Web3-Pi/Web3-Pi-UPS/docs/images/renders/front_3.png

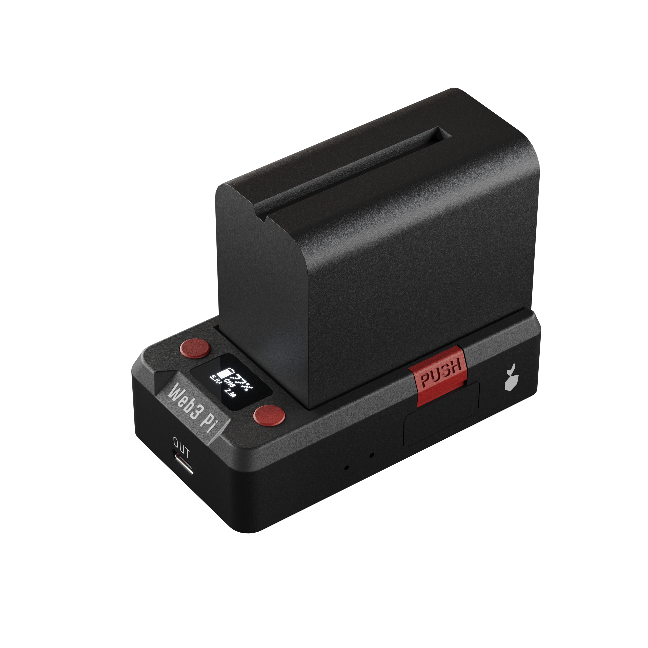
docs/images/renders/front_3.png
