Web3-Pi/Web3-Pi-UPS/firmware-ESP32-LTE-M/docs/SIM7080_1.jpg.webp

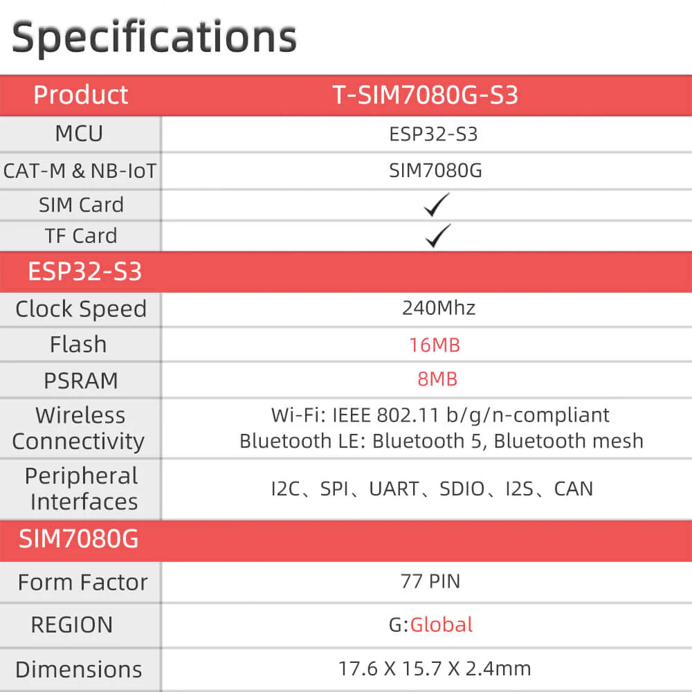
firmware-ESP32-LTE-M/docs/SIM7080_1.jpg.webp
