Web3-Pi/Web3-Pi-UPS/firmware-ESP32-LTE-M/docs/SIM7080_2_1.jpg.webp

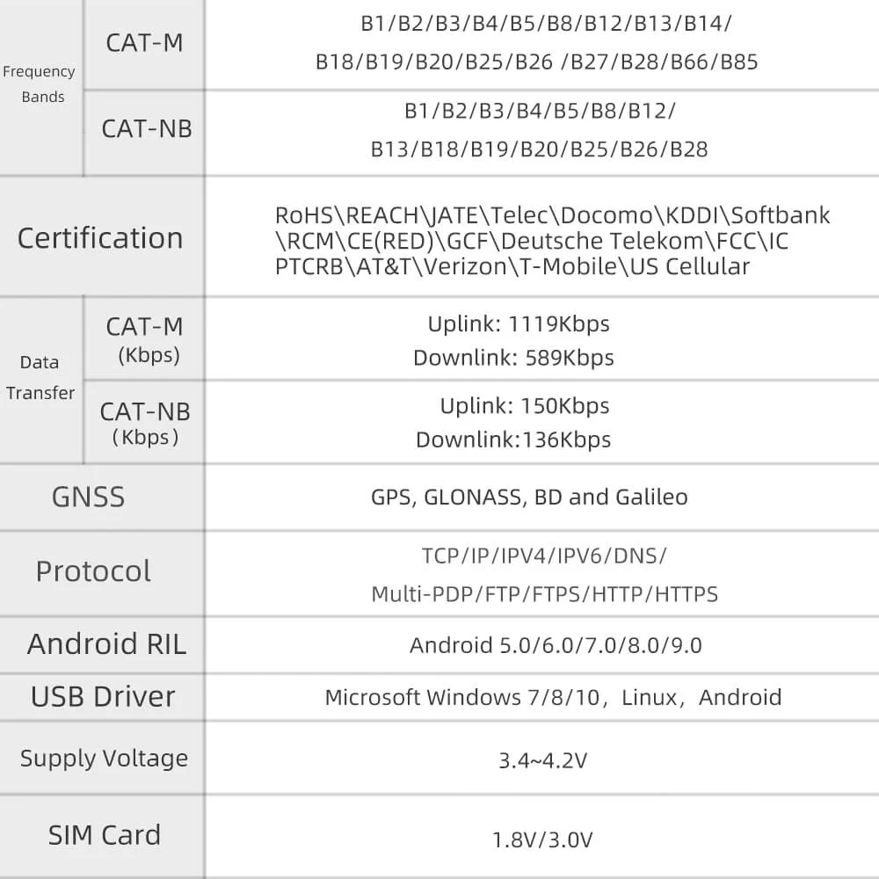
firmware-ESP32-LTE-M/docs/SIM7080_2_1.jpg.webp
