Web3-Pi/Web3-Pi-UPS/firmware-ESP32-LTE-M/docs/T-SIM7080G-S3-H606_8.jpg

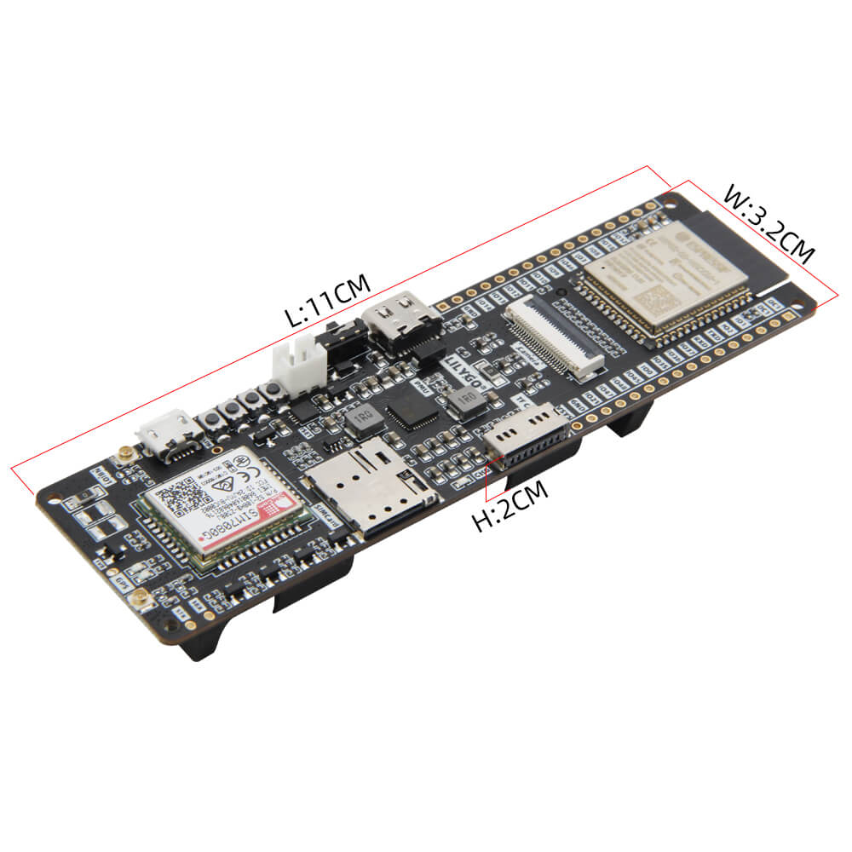
firmware-ESP32-LTE-M/docs/T-SIM7080G-S3-H606_8.jpg
