Web3-Pi/Web3-Pi-UPS/firmware-ESP32-LTE-M/docs/T-SIM7080G_Schematic.pdf

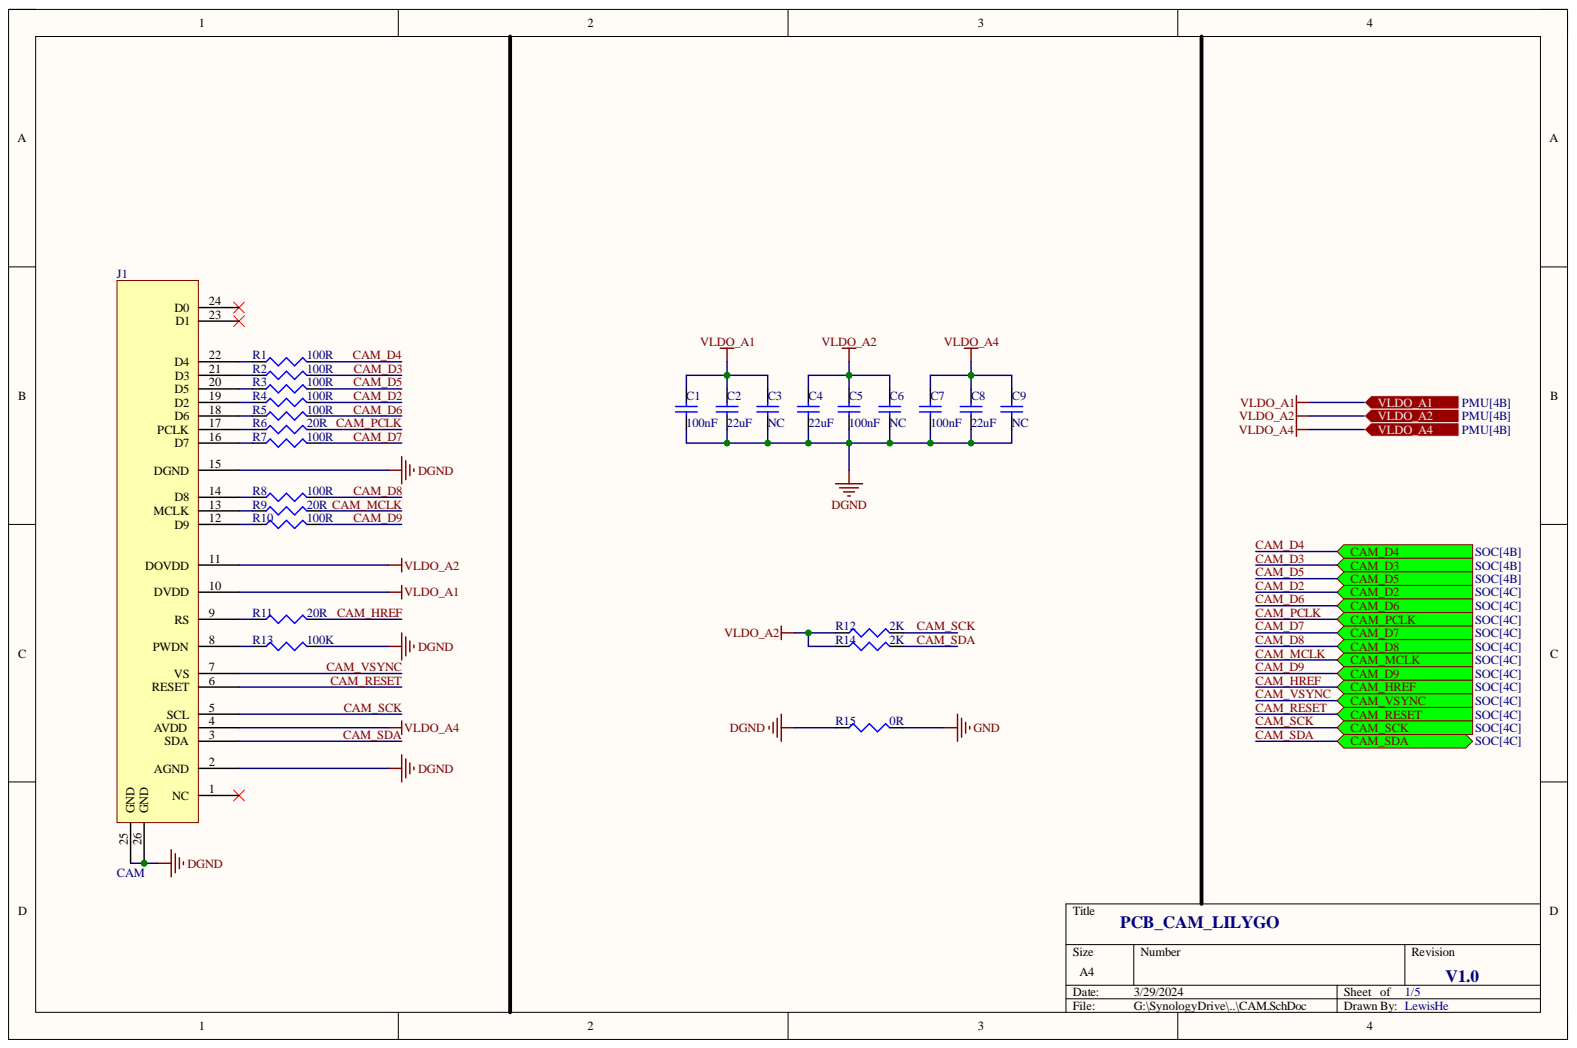
[picture p45: page 1]

Siz e A4 | Numb e r | R evisio n V1.

Da te : 3/29/202 4 | She et of
File : G:\SynologyDrive\. .\C AM . S c hD o c | Dr awn B y : Lewi s H e

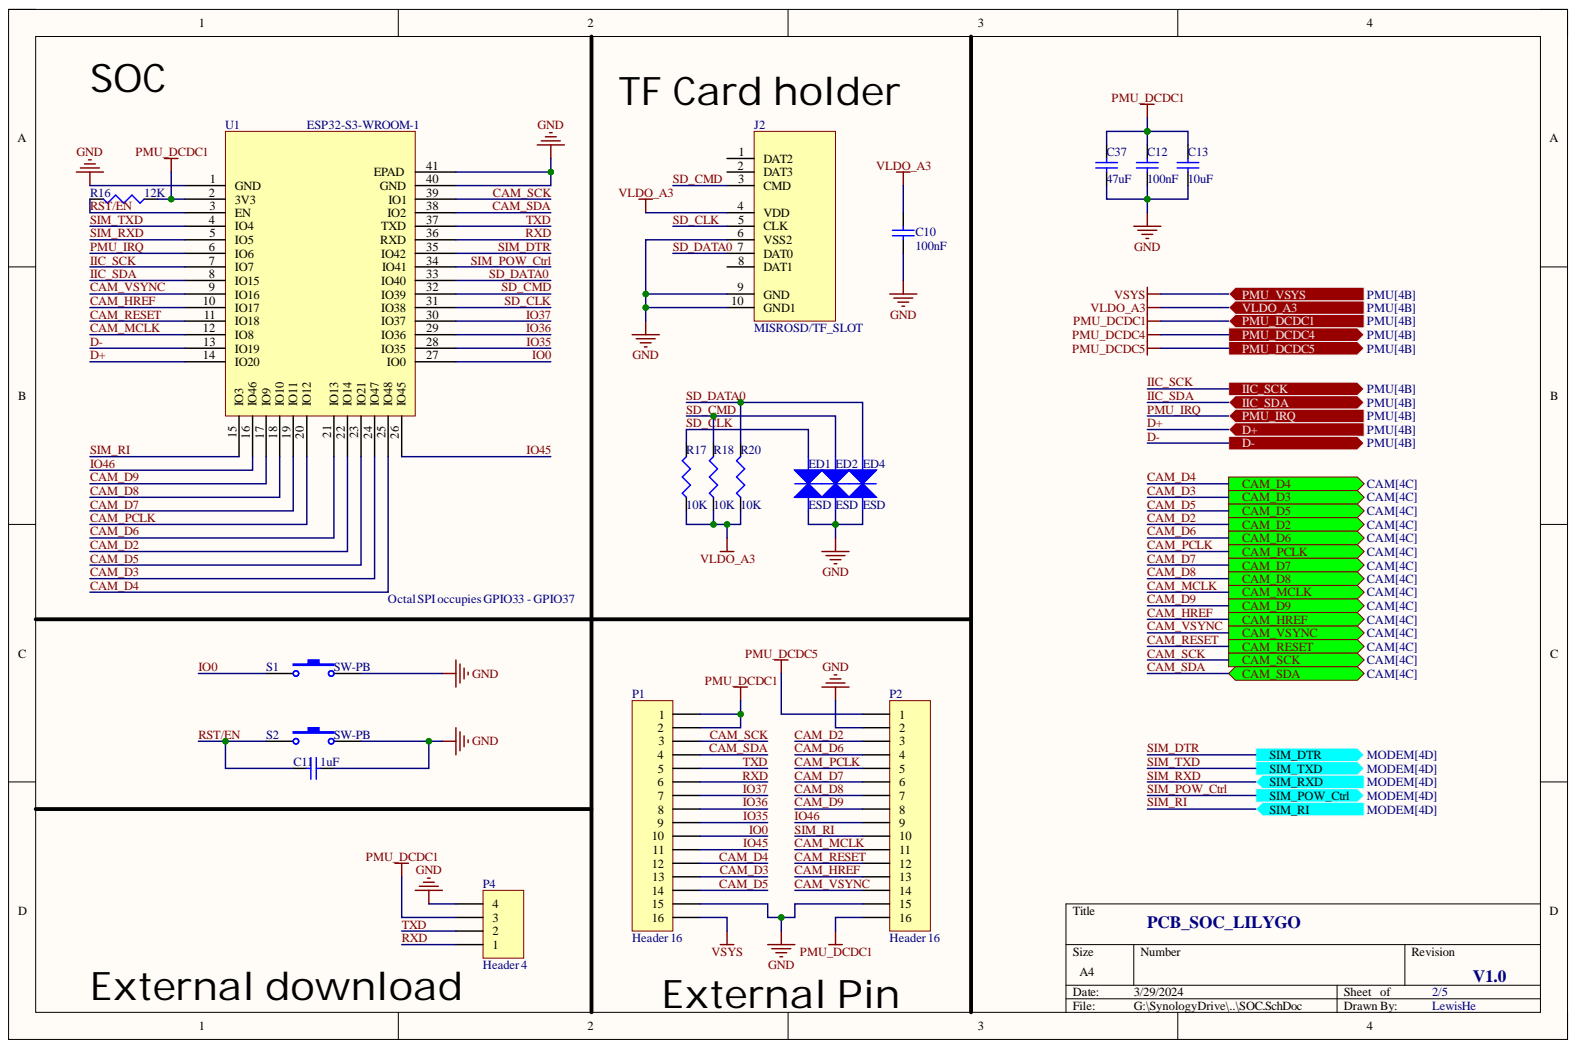
[picture p46: page 2]

2 | | CAM_S C K
3 | | CAM_S D A

Da te : 3/29/202 4 | She et of
File : G:\SynologyDrive\. .\S O C . S c hD o c | Dr awn B y : Lewi s H e

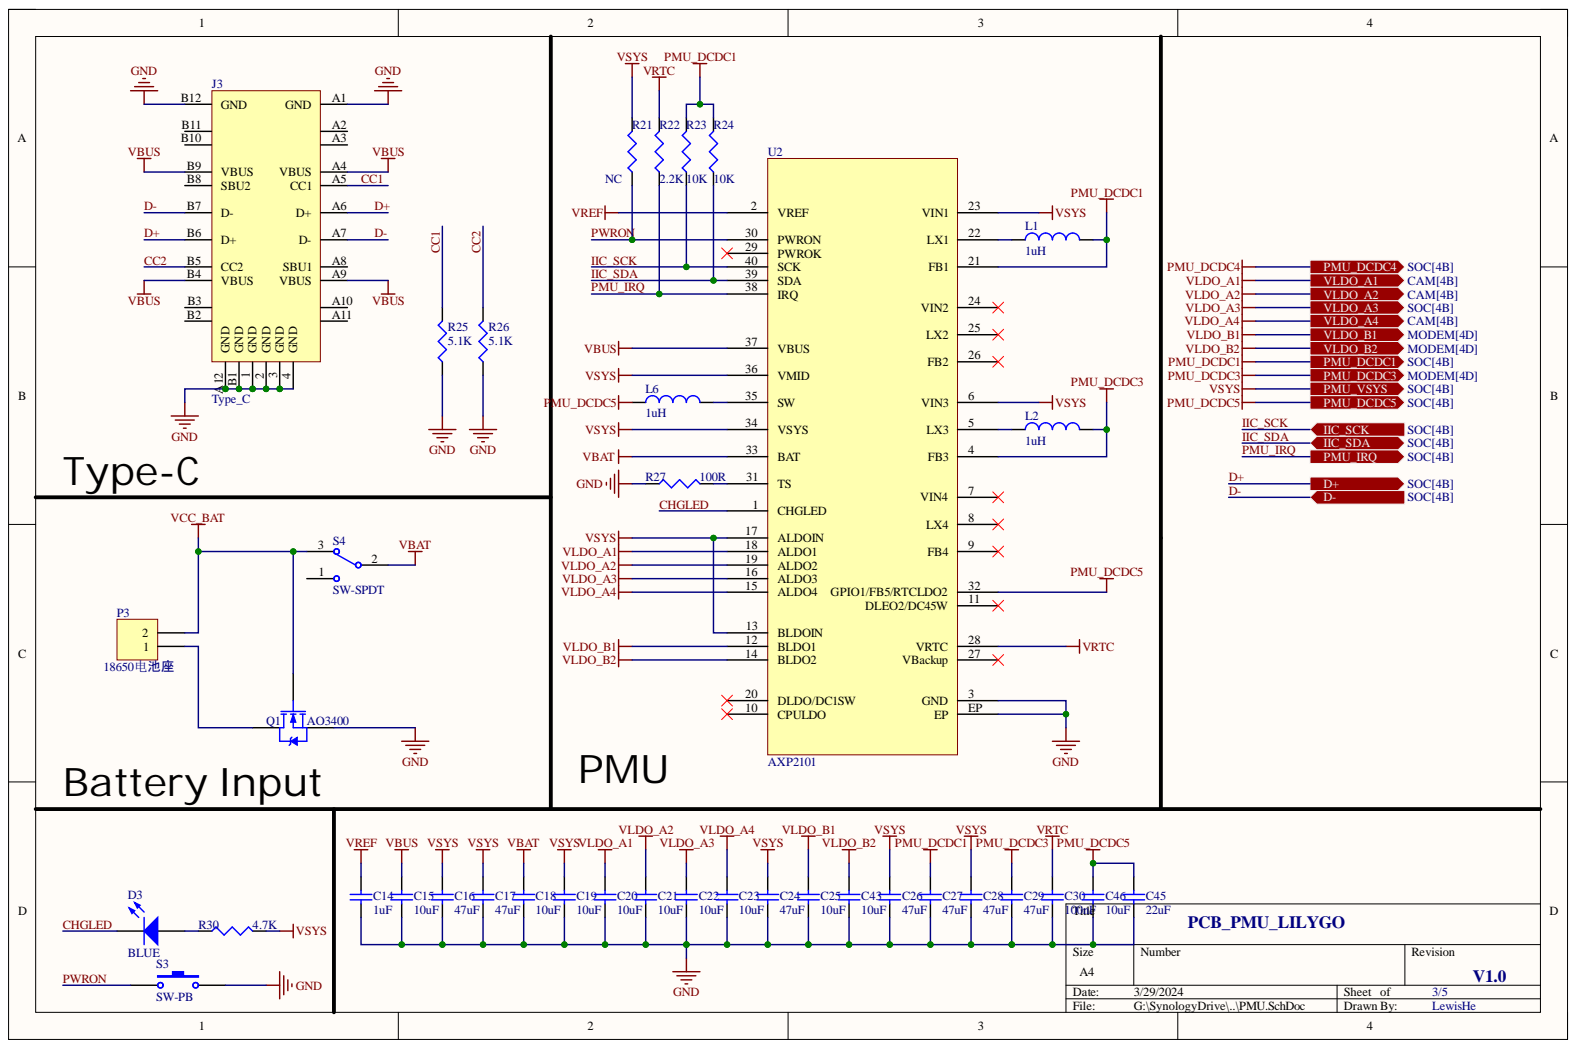
[picture p47: page 3]

ALDO1 18

ALDO4 15 ALDO3 16

BLDO1 12 BLDOIN 13

Date: 3/29/2024 | Sheet of
File: G:\SynologyDrive\..\PMU.SchDoc | Drawn By: LewisHe

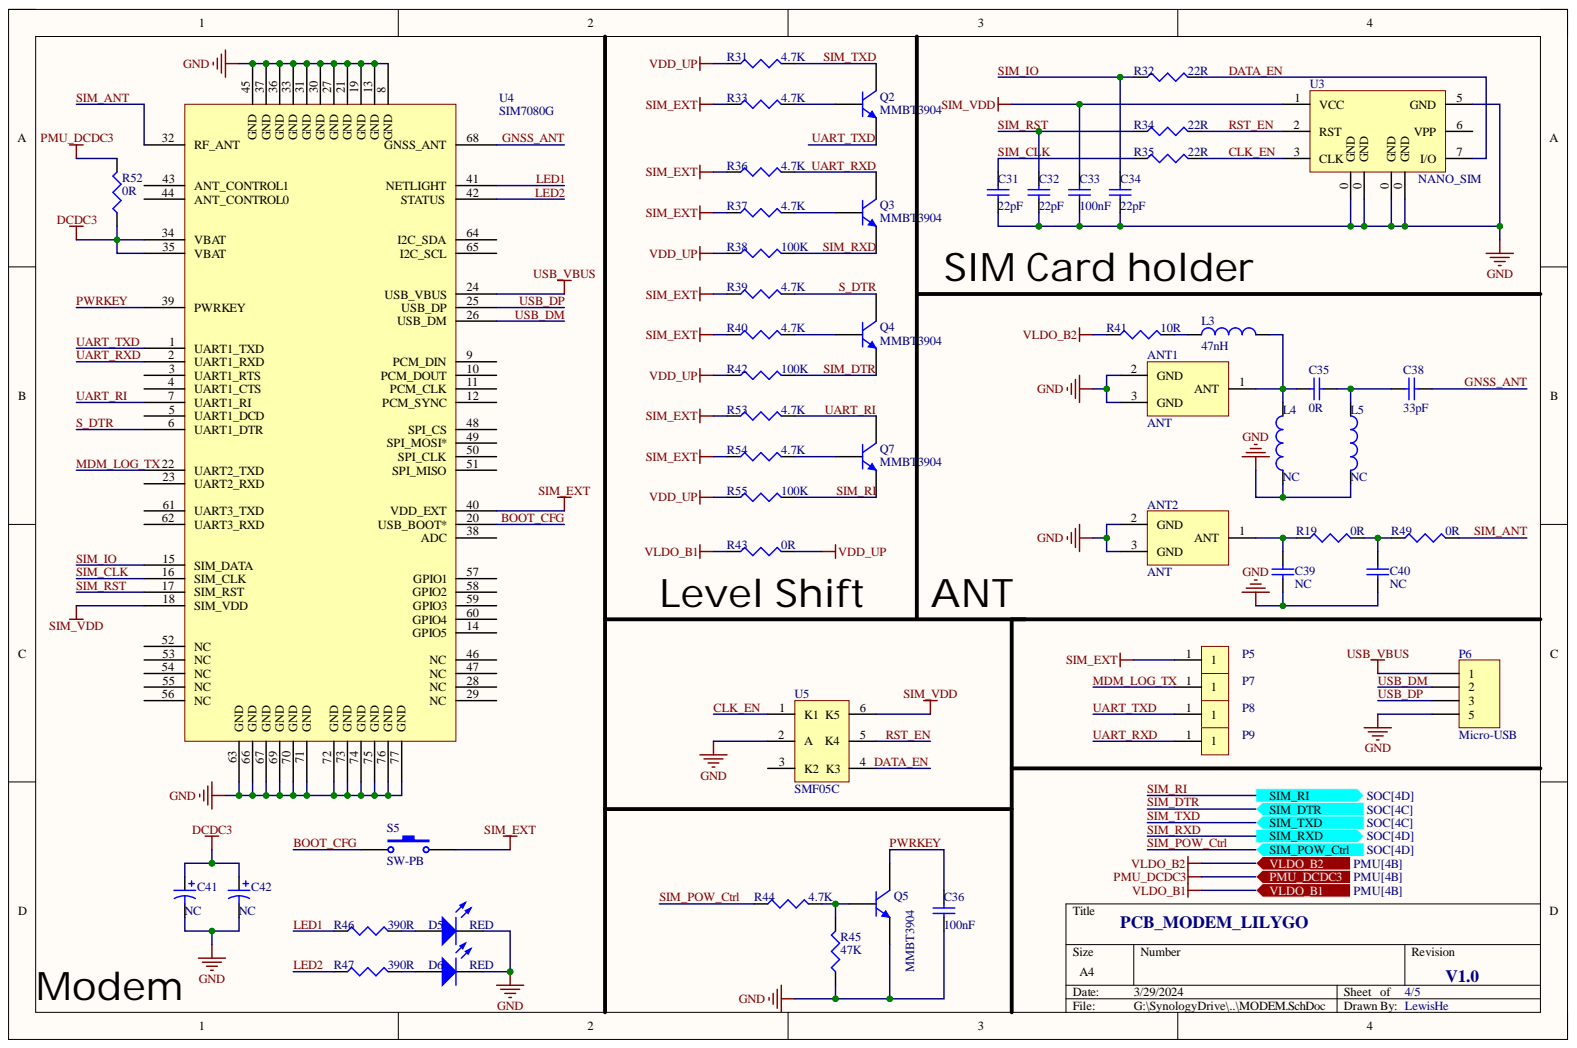
[picture p48: page 4]

Siz e A4 | Numb e r | R evisio n V1.

Da te : 3/29/202 4 | She et of
File : G:\SynologyDrive\. .\MO D EM . S c hD o c | Dr awn B y :

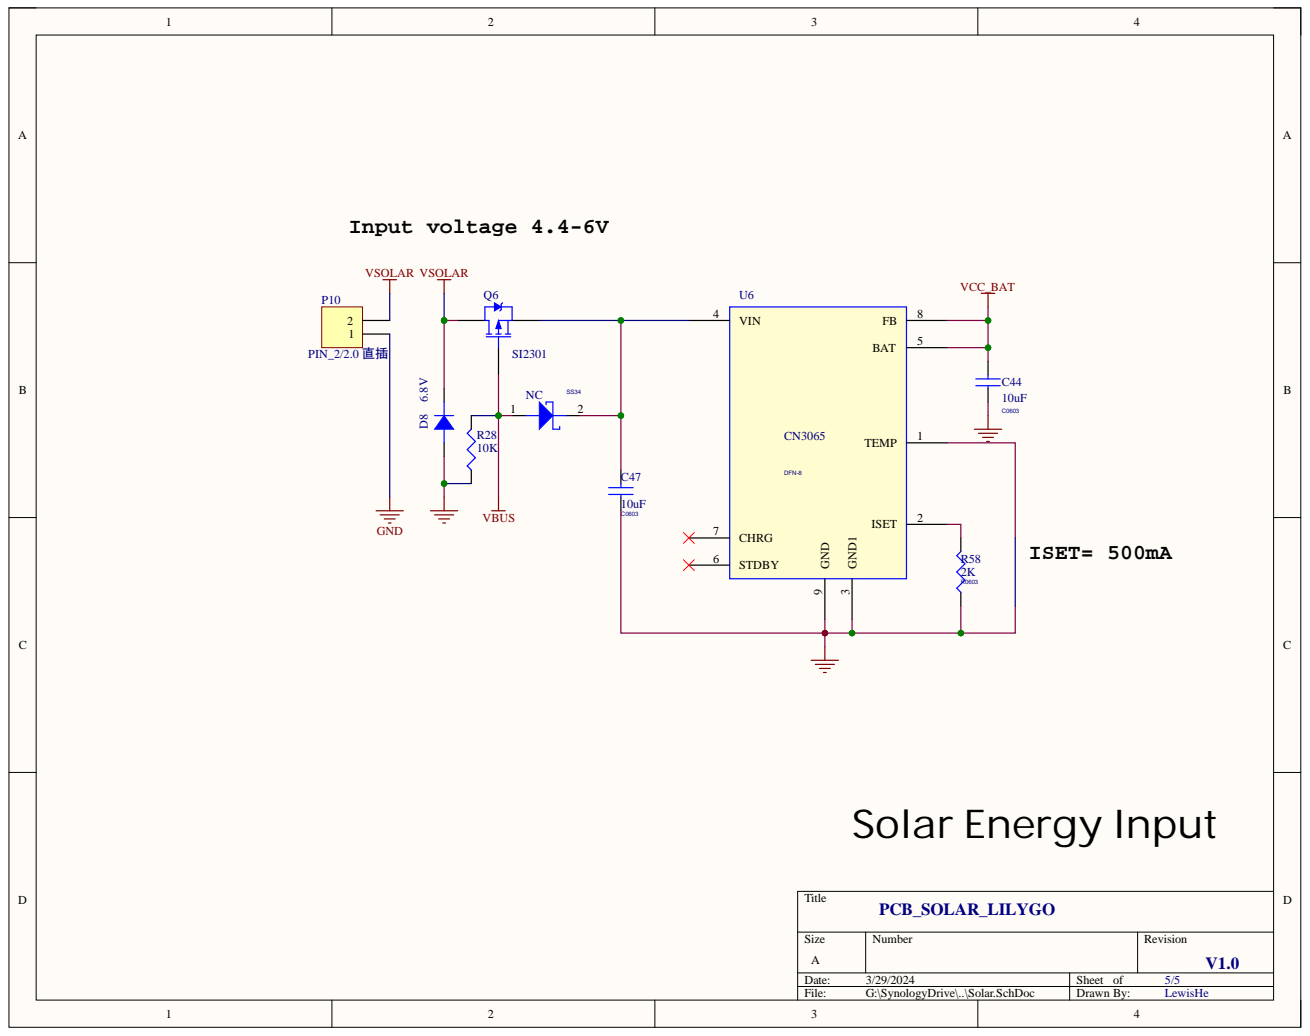
[picture p49: page 5]
