Web3-Pi/Web3-Pi-UPS/firmware-ESP32-LTE-M/main/fw_ota.c

/*
 * OTA-1 — firmware update engine. See fw_ota.h for the three paths.
 *
 * Path 1 (self-OTA over LTE): WS-9 net.fw_update REQ → validate + ACK
 * (result byte on t/{iccid}/cmd/response) → download task streams the image
 * over HTTPS (esp_https_ota advanced API, cert bundle, redirects followed)
 * into the passive OTA slot → SHA-256 read-back of the written bytes is
 * compared against the commanded digest → esp_https_ota_finish flips the
 * boot partition → reboot. The freshly booted image is PENDING_VERIFY
 * (CONFIG_BOOTLOADER_APP_ROLLBACK_ENABLE) until the uplink proves healthy.
 *
 * Path 2 (fw_xfer receiver, Workbench over USB): net.fw_xfer_begin/data/end
 * REQs land here from wups_link's dispatch; esp_ota_* writes the passive
 * slot, END(commit=1) runs the SAME read-back verify, then set-boot +
 * reboot. The rebooted image goes through the identical PENDING_VERIFY /
 * mark-valid-on-healthy-uplink rollback machinery — full safety net.
 *
 * Path 3 (RP2040 relay over LTE): net.fw_update target=RP2040 → relay task
 * streams the image over HTTPS chunk-by-chunk and drives the fw_xfer sender
 * over the UART link (strict stop-and-wait), hashing the stream on the fly;
 * END(commit=1) is only sent when the digest matches the commanded sha256.
 */

#include "fw_ota.h"
#include "fw_ota_http_policy.h"
#include "arkiv_ack.h"
#include "backend_mode.h"
#include "identity.h"
#include "modem.h"
#include "mqtt.h"
#include "wups_link.h"
#include "wups_proto.h"

#include <inttypes.h>
#include <stdarg.h>
#include <stdio.h>
#include <stdlib.h>
#include <string.h>

#include "esp_crt_bundle.h"
#include "esp_http_client.h"
#include "esp_https_ota.h"
#include "esp_log.h"
#include "esp_ota_ops.h"
#include "esp_partition.h"
#include "esp_system.h"
#include "esp_timer.h"
#include "esp_tls_errors.h"
#include "freertos/FreeRTOS.h"
#include "freertos/semphr.h"
#include "freertos/task.h"
/* IDF 6.0 / mbedtls 4.x: the low-level mbedtls_sha256_* API is the project
 * convention (the mbedtls_md_* wrapper fails at runtime here — see
 * http_backend.c). legacy sha256.h moved under mbedtls/private/. */
#define MBEDTLS_DECLARE_PRIVATE_IDENTIFIERS
#include <mbedtls/private/sha256.h>

#define TAG "fw_ota"

/* URL cap = what physically fits in one net.fw_update frame. */
#define FW_OTA_URL_MAX \
    (WUPS_MAX_PAYLOAD - sizeof(wups_net_fw_update_v1_hdr_t))   /* 168 */

/* Per-socket-op timeout. FW_OTA_TIMEOUT_S is also checked between SDK
 * operations across all retries; it is not an asynchronous cancellation. */
#define FW_OTA_HTTP_TIMEOUT_MS  30000

/* SHA-256 read-back chunk (one flash sector). */
#define FW_OTA_READBACK_CHUNK   4096
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
